JEly613/Mini-LiDAR-Board/firmware/src/util.c

/* ---------------------------------------------------------------------------
 * util.c -- minimal freestanding libc shims.  See util.h for why these exist.
 *
 * These are deliberately simple byte loops.  Every call site in this firmware
 * copies at most a few hundred bytes (USB descriptors, packet buffers), so the
 * word-at-a-time cleverness a real libc uses would buy nothing measurable and
 * would cost readability.
 * ------------------------------------------------------------------------- */

#include "util.h"

void *memcpy(void *dst, const void *src, size_t n)
{
    unsigned char       *d = (unsigned char *)dst;
    const unsigned char *s = (const unsigned char *)src;

    while (n--) {
        *d++ = *s++;
    }
    return dst;
}

void *memmove(void *dst, const void *src, size_t n)
{
    unsigned char       *d = (unsigned char *)dst;
    const unsigned char *s = (const unsigned char *)src;

    if (d == s || n == 0U) {
        return dst;
    }
    if (d < s) {
        while (n--) {
            *d++ = *s++;
        }
    } else {
        /* Overlapping and moving upwards: copy backwards. */
        d += n;
        s += n;
        while (n--) {
            *--d = *--s;
        }
    }
    return dst;
}

void *memset(void *dst, int c, size_t n)
{
    unsigned char *d = (unsigned char *)dst;

    while (n--) {
        *d++ = (unsigned char)c;
    }
    return dst;
}

int memcmp(const void *a, const void *b, size_t n)
{
    const unsigned char *p = (const unsigned char *)a;
    const unsigned char *q = (const unsigned char *)b;

    while (n--) {
        if (*p != *q) {
            return (int)*p - (int)*q;
        }
        p++;
        q++;
    }
    return 0;
}

size_t strlen(const char *s)
{
    const char *p = s;

    while (*p != '\0') {
        p++;
    }
    return (size_t)(p - s);
}
